sanderboer/chonkybois/img/IMG_3469.jpg

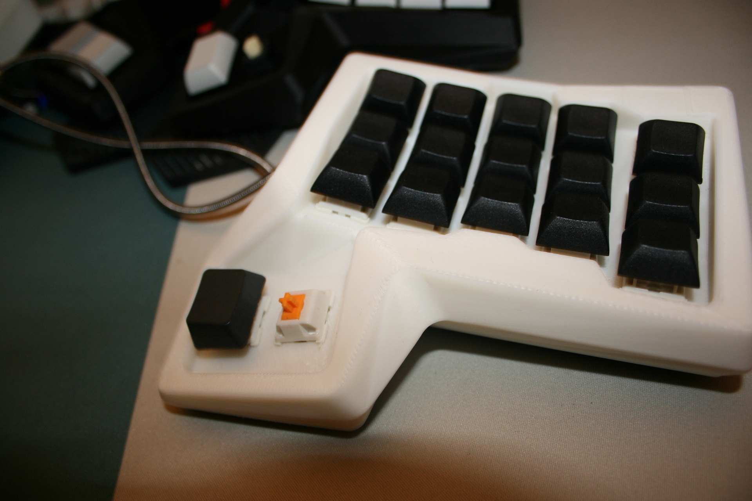
img/IMG_3469.jpg
