sanderboer/chonkybois/img/IMG_3470.jpg

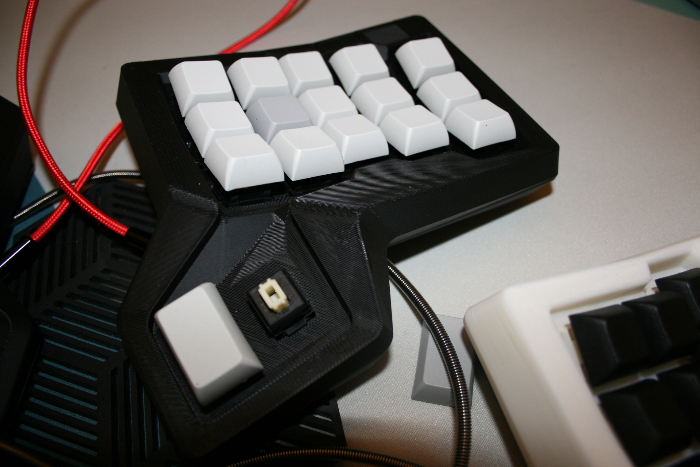
img/IMG_3470.jpg
