sanderboer/chonkybois/img/IMG_3471.jpg

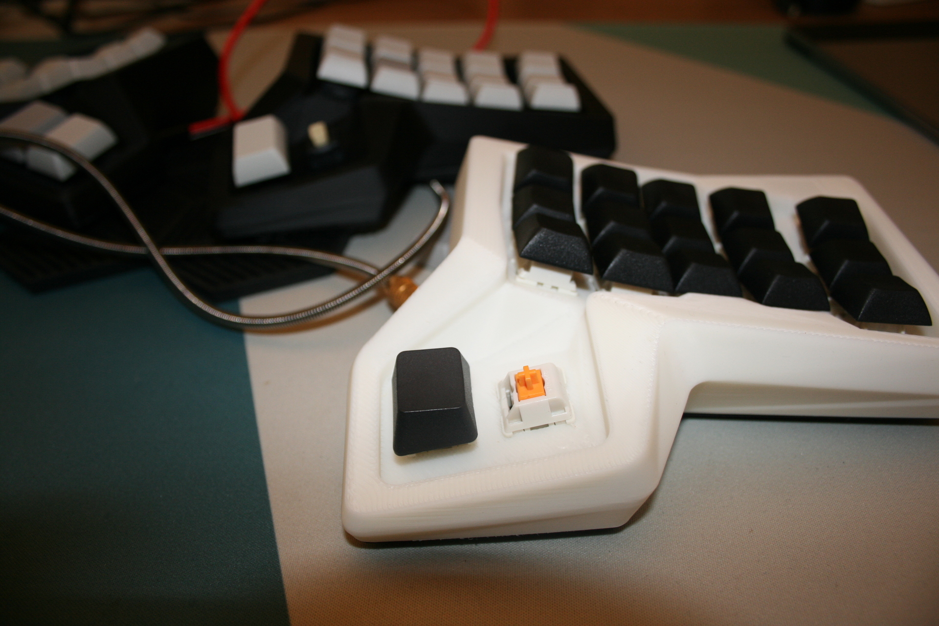
img/IMG_3471.jpg
