sanderboer/chonkybois/img/IMG_3472.jpg

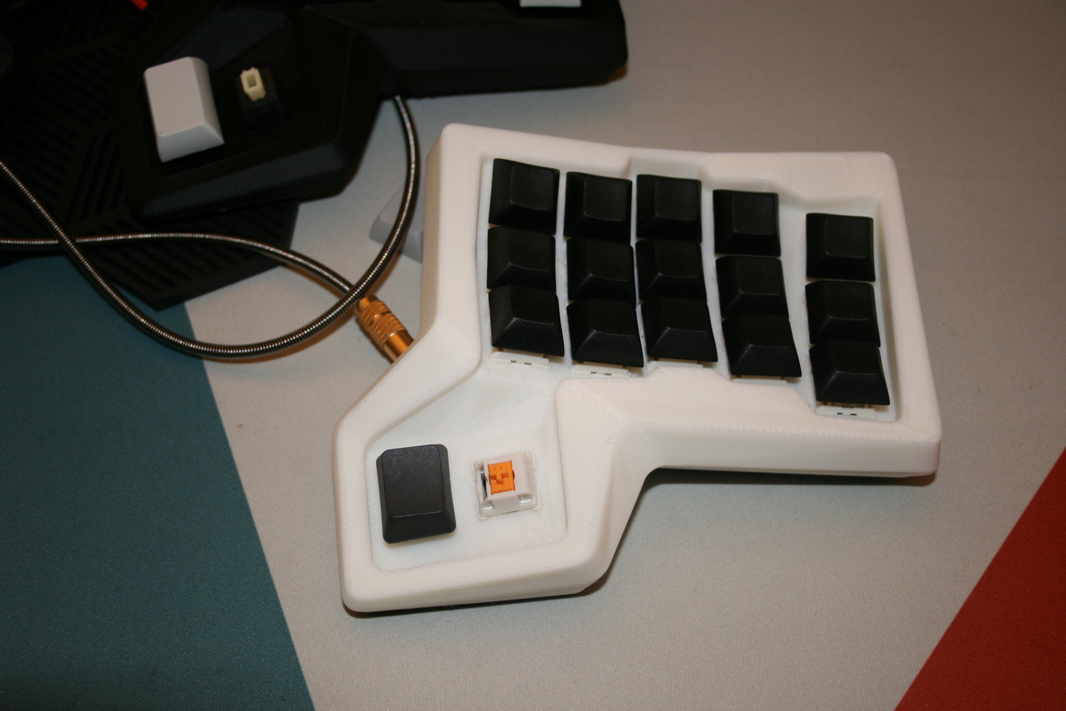
img/IMG_3472.jpg
