sanderboer/chonkybois/img/IMG_3473.jpg

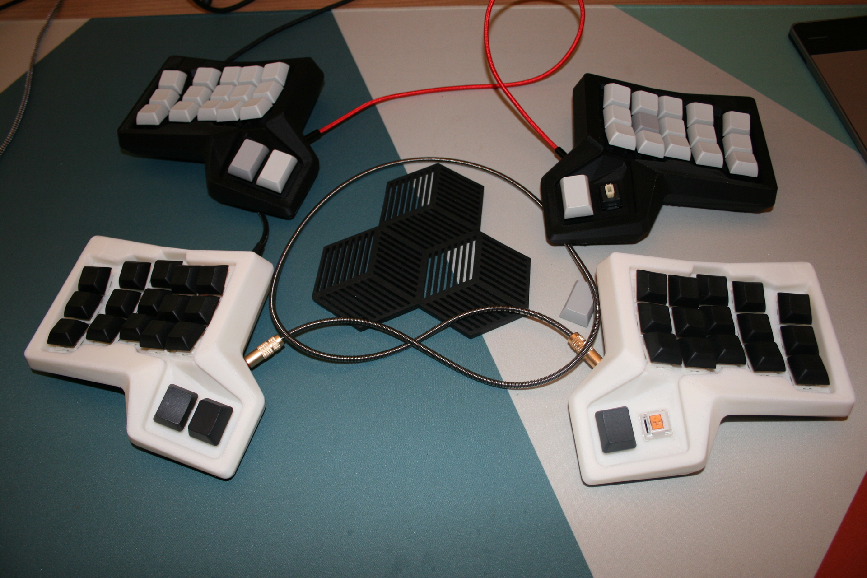
img/IMG_3473.jpg
