sanderboer/chonkybois/img/IMG_3477.jpg

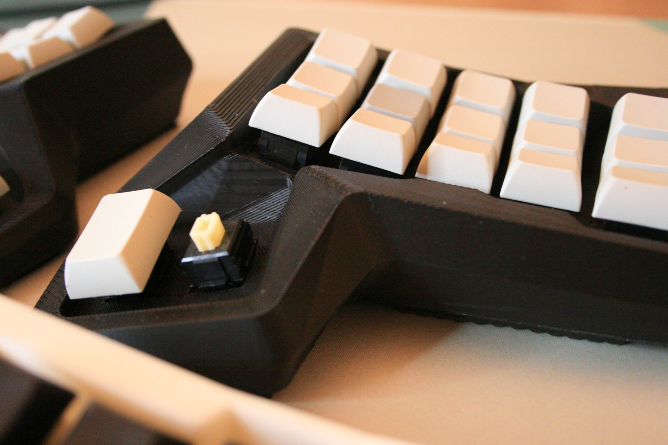
img/IMG_3477.jpg
