sanderboer/chonkybois/stl_wireless/case_bot_left_wireless_nulb7.stl

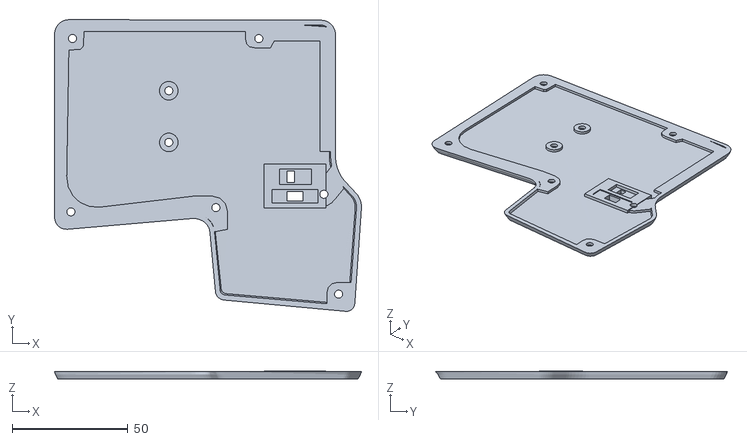
[picture p31: CAD file, 2021-07-21]
stl_wireless/case_bot_left_wireless_nulb7.stl
132.4 x 125.8 x 3.49
