sanderboer/chonkybois/stl_wired/ALPS-case_top_right_wired.stl

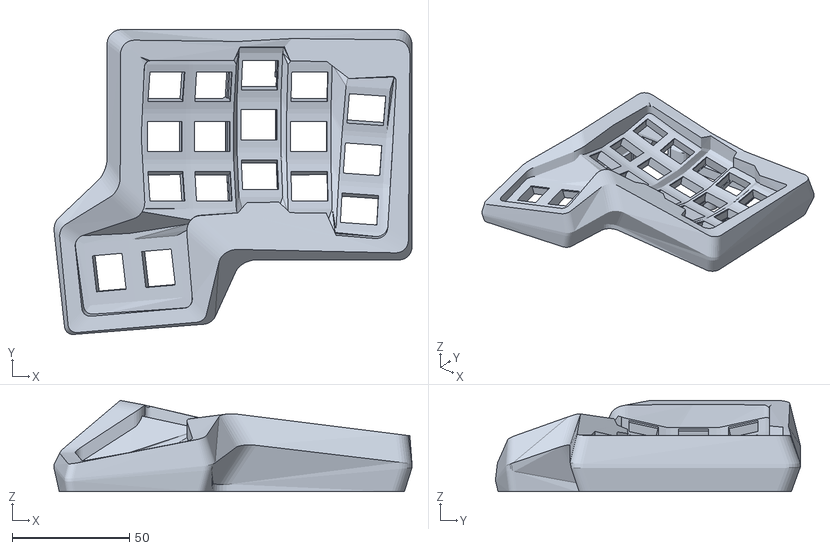
[picture p32: CAD file, 2021-07-20]
stl_wired/ALPS-case_top_right_wired.stl
152.7 x 130.0 x 38.9
