sanderboer/chonkybois/stl_wireless/case_top_left_wireless_nulb7.stl

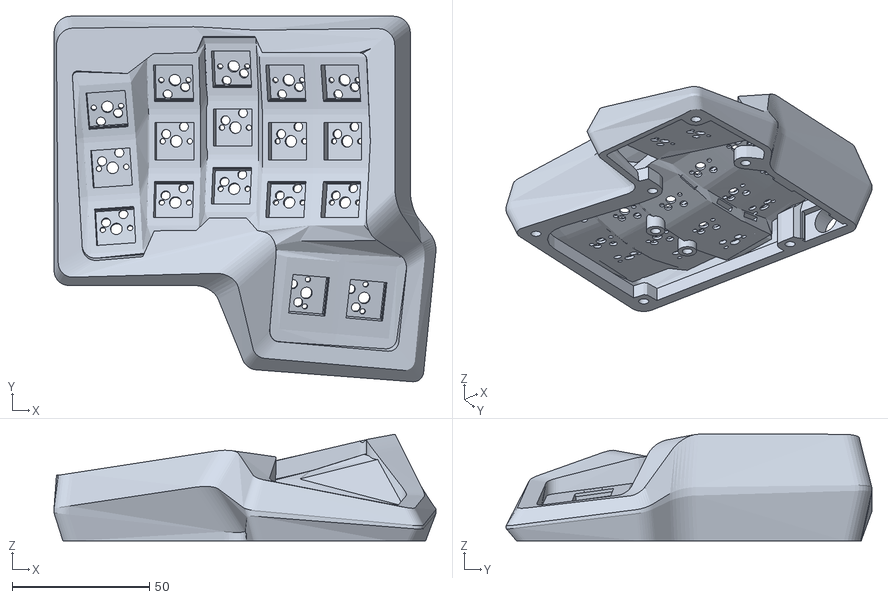
[picture p33: CAD file, 2021-07-21]
stl_wireless/case_top_left_wireless_nulb7.stl
139.4 x 133.4 x 38.9
