sanderboer/chonkybois/stl_wired/case_bot_right_wired.stl

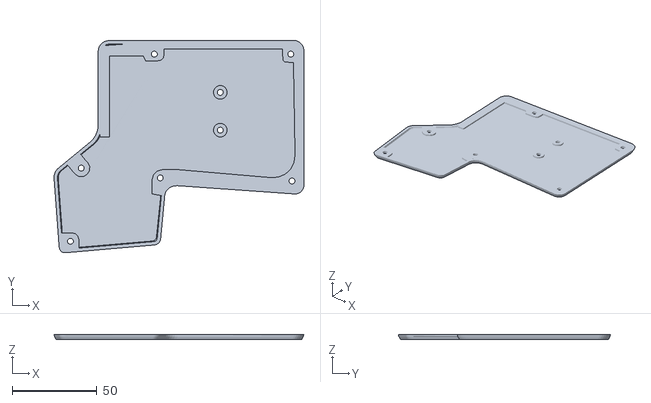
[picture p35: CAD file, 2021-07-20]
stl_wired/case_bot_right_wired.stl
147.2 x 125.1 x 3.18
