sanderboer/chonkybois/stl_wired/case_top_right_wired.stl

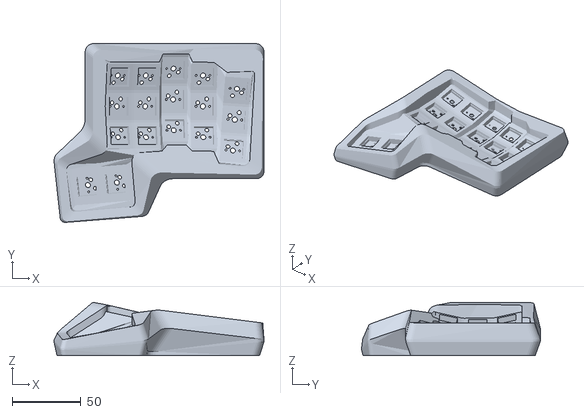
[picture p36: CAD file, 2021-07-20]
stl_wired/case_top_right_wired.stl
152.7 x 130.0 x 38.9
