sanderboer/chonkybois/stl_wired/Holder-Promicro_x2.stl

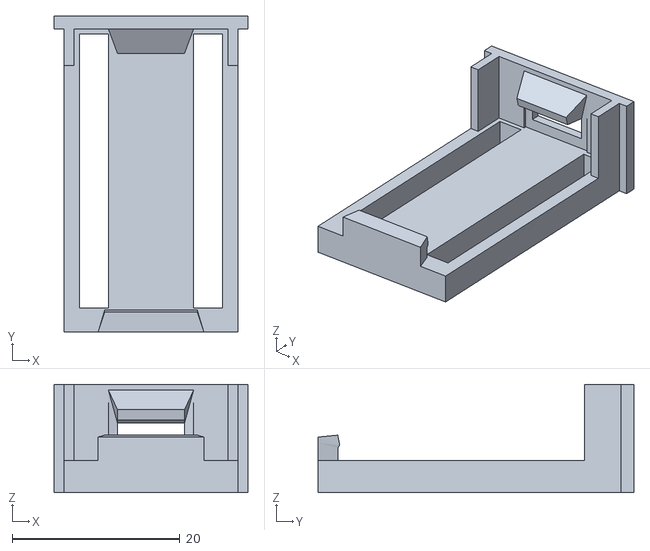
[picture p37: CAD file, 2021-06-23]
stl_wired/Holder-Promicro_x2.stl
23.1 x 37.7 x 12.9
