sanderboer/chonkybois/stl_wireless/case_bot_left_wireless.stl

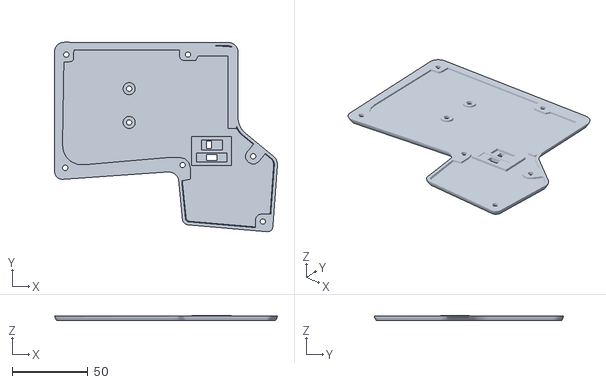
[picture p38: CAD file, 2021-07-20]
stl_wireless/case_bot_left_wireless.stl
147.2 x 125.1 x 3.49
