sanderboer/chonkybois/stl_wireless/Holder-bluemicro840_x2.stl

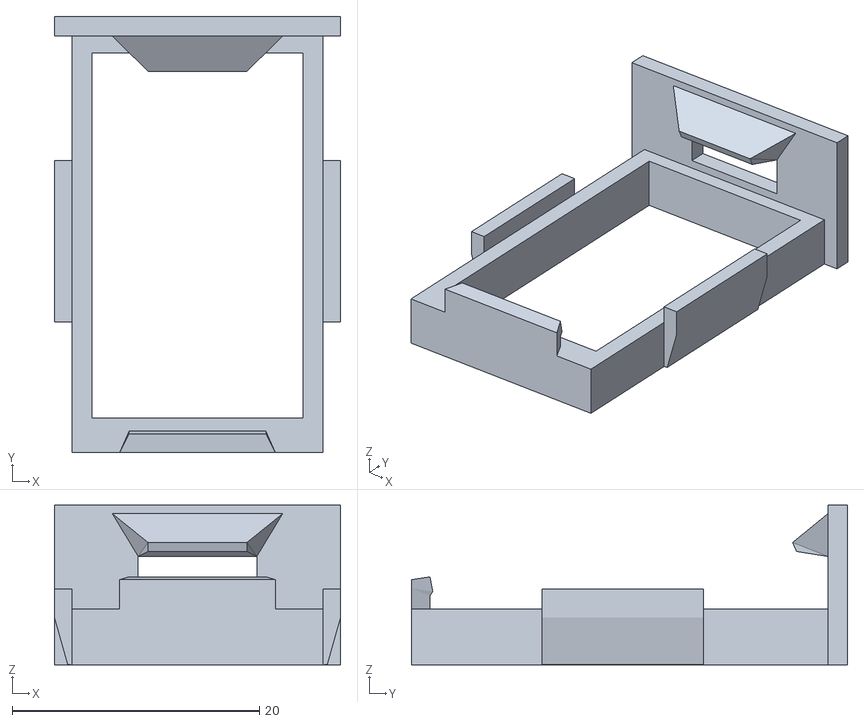
[picture p39: CAD file, 2021-07-20]
stl_wireless/Holder-bluemicro840_x2.stl
23.1 x 35.3 x 12.9
