sanderboer/chonkybois/stl_wireless/Holder-bluemacro840_x2.stl

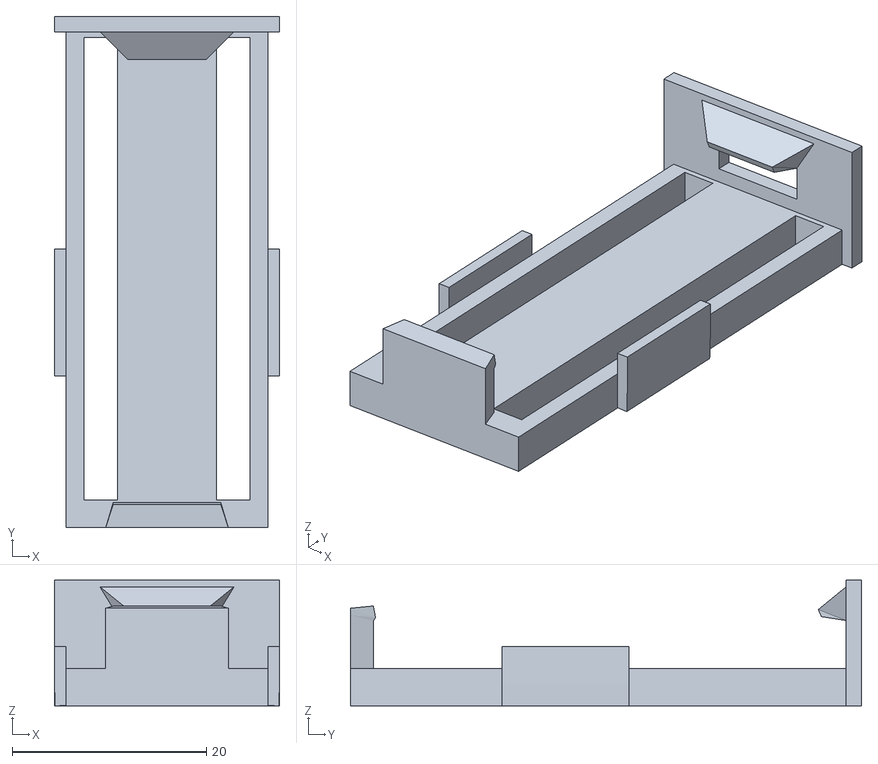
[picture p40: CAD file, 2021-07-20]
stl_wireless/Holder-bluemacro840_x2.stl
23.1 x 52.6 x 12.9
